mpinnuck/PiDjiRc2KmzSync/mechanical/Circuit/PiRCS2Updater/PiRCS2Updater-simple.kicad_sch

## KiCad design mechanical/Circuit/PiRCS2Updater/PiRCS2Updater-simple.kicad_sch (2026-10-04)

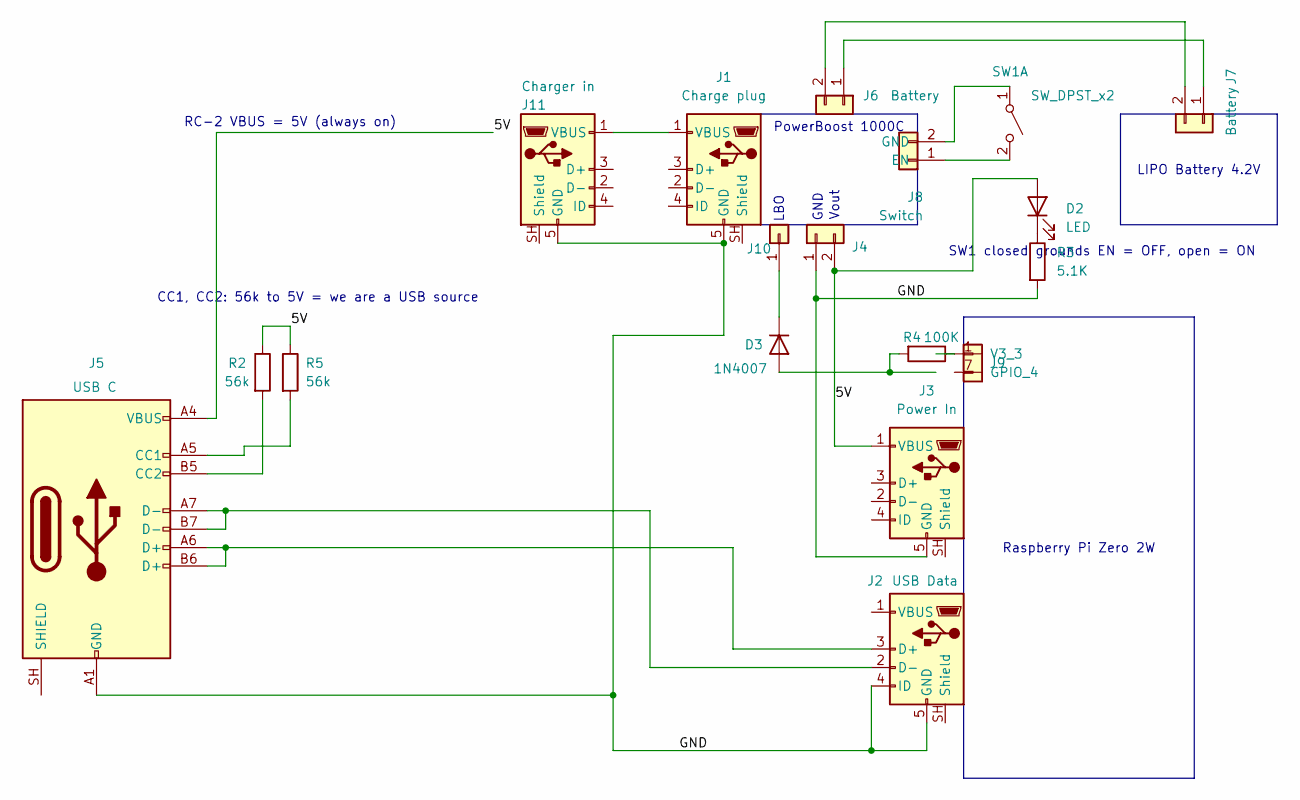
[picture p4: schematic PiRCS2Updater-simple.kicad_sch]

Parts:
D2: LED
D3: 1N4007; D_DO-41_SOD81_P10.16mm_Horizontal
J1: Charge plug
J2: USB Data
J3: Power In
J4, J9: Conn_01x02
J5: USB C
J6, J7: Battery
J8: Switch
J10: Conn_01x01
J11: Charger in
R2, R5: 56k
R3: 5.1K
R4: 100K
SW1: SW_DPST_x2

Connections:
5V: D2.2 (A), J3.1 (VBUS), J4.2, J5.A4 (VBUS), J5.A9 (VBUS), J5.B4 (VBUS), J5.B9 (VBUS), R2.1, R5.1
GND: J1.5 (GND), J2.4 (ID), J2.5 (GND), J3.5 (GND), J4.1, J5.A1 (GND), J5.A12 (GND), J5.B1 (GND), J5.B12 (GND), J11.5 (GND), R3.2
unnamed: D2.1 (K), R3.1
unnamed: D3.1 (K), J10.1
unnamed: D3.2 (A), R4.2
unnamed: J1.1 (VBUS), J11.1 (VBUS)
unnamed: J2.2 (D-), J5.A7 (D-), J5.B7 (D-)
unnamed: J2.3 (D+), J5.A6 (D+), J5.B6 (D+)
unnamed: J5.A5 (CC1), R5.2
unnamed: J5.B5 (CC2), R2.2
unnamed: J6.1, J7.1
unnamed: J6.2, J7.2
unnamed: J8.1 (EN), SW1.2 (B)
unnamed: J8.2 (GND), SW1.1 (A)
unnamed: J9.1 (V3_3), R4.1

Notes on the sheet:
SW1 closed grounds EN = OFF, open = ON
GND
RC-2 VBUS = 5V (always on)
Vout
LBO
Raspberry Pi Zero 2W
PowerBoost 1000C
LIPO Battery 4.2V
CC1, CC2: 56k to 5V = we are a USB source
