mpinnuck/PiDjiRc2KmzSync/mechanical/Circuit/PiRCS2Updater/PiRCS2Updater.kicad_sch

## KiCad design mechanical/Circuit/PiRCS2Updater/PiRCS2Updater.kicad_sch (2026-09-25)

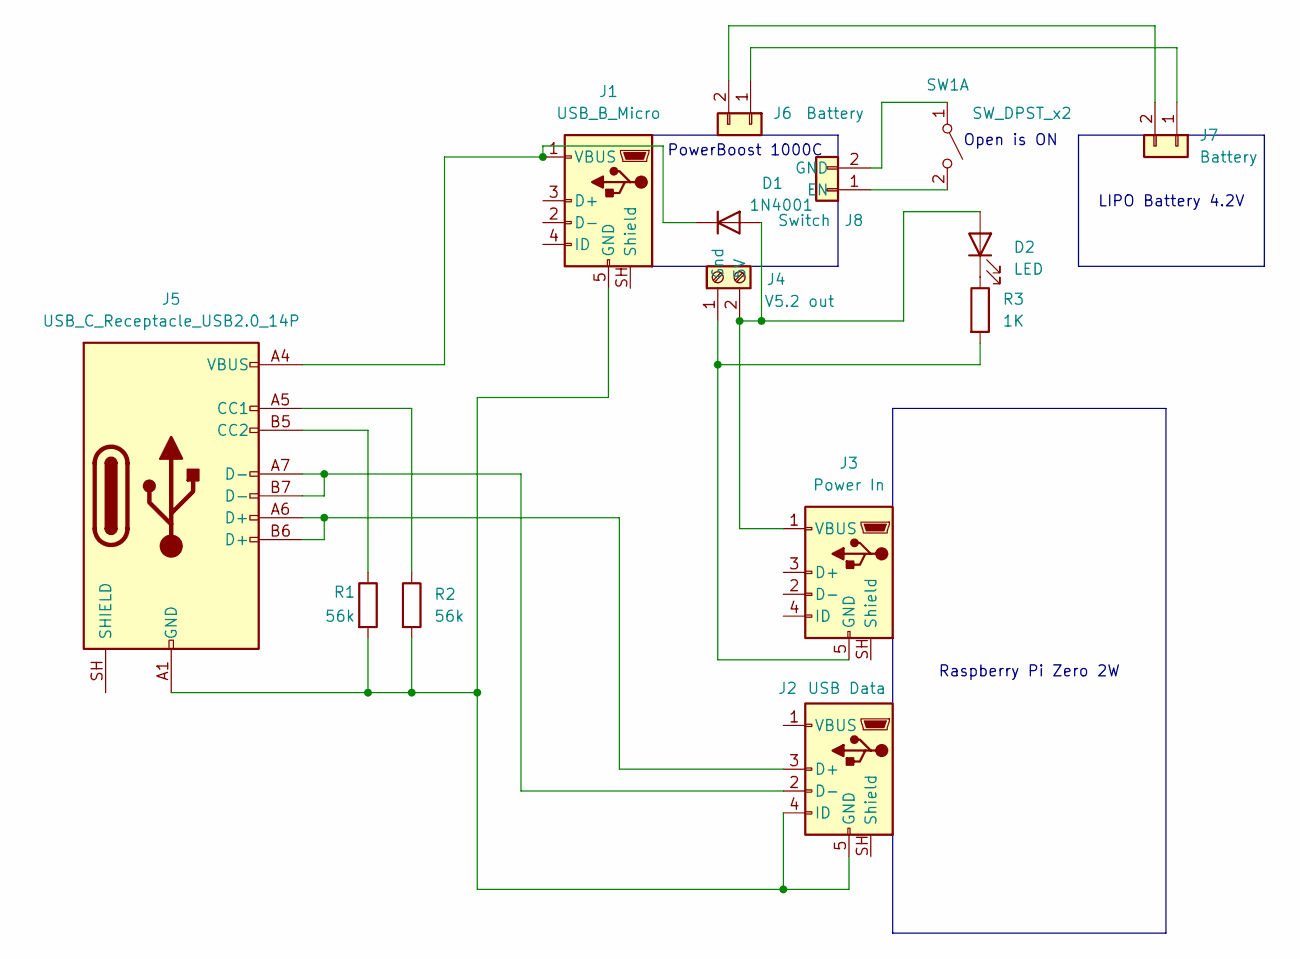
[picture p5: schematic PiRCS2Updater.kicad_sch]

Parts:
D1: 1N4001; D_DO-41_SOD81_P10.16mm_Horizontal
D2: LED
J1: USB_B_Micro
J2: USB Data
J3: Power In
J4: V5.2 out
J5: USB_C_Receptacle_USB2.0_14P
J6, J7: Battery
J8: Switch
R1, R2: 56k
R3: 1K
SW1: SW_DPST_x2

Connections:
unnamed: D1.1 (K), J1.1 (VBUS), J5.A4 (VBUS), J5.A9 (VBUS), J5.B4 (VBUS), J5.B9 (VBUS)
unnamed: D1.2 (A), D2.2 (A), J3.1 (VBUS), J4.2 (5V)
unnamed: D2.1 (K), R3.1
unnamed: J1.5 (GND), J2.4 (ID), J2.5 (GND), J5.A1 (GND), J5.A12 (GND), J5.B1 (GND), J5.B12 (GND), R1.2, R2.2
unnamed: J2.2 (D-), J5.A7 (D-), J5.B7 (D-)
unnamed: J2.3 (D+), J5.A6 (D+), J5.B6 (D+)
unnamed: J3.5 (GND), J4.1 (Gnd), R3.2
unnamed: J5.A5 (CC1), R2.1
unnamed: J5.B5 (CC2), R1.1
unnamed: J6.1, J7.1
unnamed: J6.2, J7.2
unnamed: J8.1 (EN), SW1.2 (B)
unnamed: J8.2 (GND), SW1.1 (A)

Notes on the sheet:
Open is ON
Raspberry Pi Zero 2W
PowerBoost 1000C
LIPO Battery 4.2V
