mpinnuck/PiDjiRc2KmzSync/mechanical/Circuit/PiRCS2Updater/xPiRCS2Updater.kicad_sch

## KiCad design mechanical/Circuit/PiRCS2Updater/xPiRCS2Updater.kicad_sch (2026-10-04)

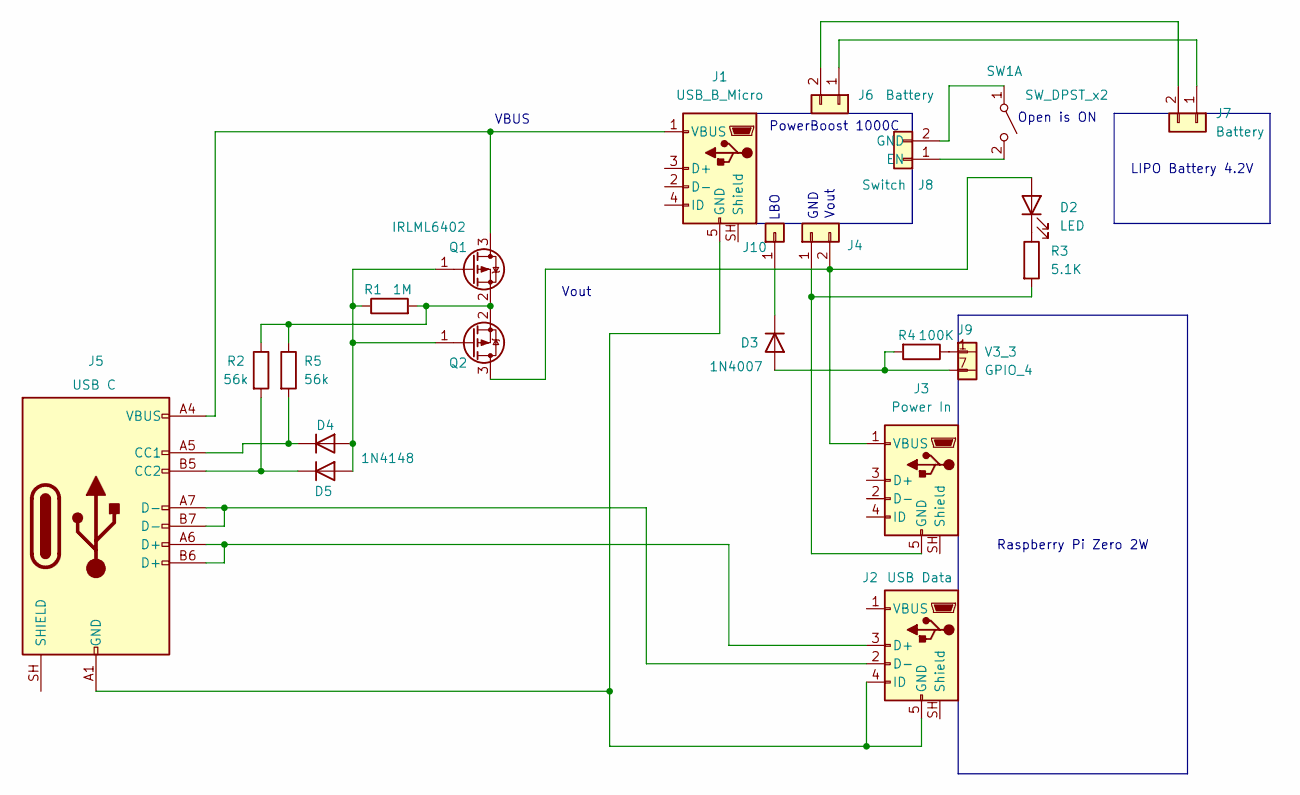
[picture p6: schematic xPiRCS2Updater.kicad_sch]

Parts:
D2: LED
D3: 1N4007; D_DO-41_SOD81_P10.16mm_Horizontal
D4, D5: 1N4148; D_DO-35_SOD27_P7.62mm_Horizontal
J1: USB_B_Micro
J2: USB Data
J3: Power In
J4, J9: Conn_01x02
J5: USB C
J6, J7: Battery
J8: Switch
J10: Conn_01x01
Q1, Q2: IRLML6402; SOT-23
R1: 1M
R2, R5: 56k
R3: 5.1K
R4: 100K
SW1: SW_DPST_x2

Connections:
unnamed: D2.1 (K), R3.1
unnamed: D2.2 (A), J3.1 (VBUS), J4.2
unnamed: D3.1 (K), J10.1
unnamed: D3.2 (A), J9.7 (GPIO_4), R4.2
unnamed: D4.1 (K), J5.A5 (CC1), R5.2
unnamed: D4.2 (A), D5.2 (A), Q1.1 (G), Q2.1 (G), R1.1
unnamed: D5.1 (K), J5.B5 (CC2), R2.2
unnamed: J1.1 (VBUS), J5.A4 (VBUS), J5.A9 (VBUS), J5.B4 (VBUS), J5.B9 (VBUS), Q1.3 (D)
unnamed: J1.5 (GND), J2.4 (ID), J2.5 (GND), J5.A1 (GND), J5.A12 (GND), J5.B1 (GND), J5.B12 (GND)
unnamed: J2.2 (D-), J5.A7 (D-), J5.B7 (D-)
unnamed: J2.3 (D+), J5.A6 (D+), J5.B6 (D+)
unnamed: J3.5 (GND), J4.1, R3.2
unnamed: J6.1, J7.1
unnamed: J6.2, J7.2
unnamed: J8.1 (EN), SW1.2 (B)
unnamed: J8.2 (GND), SW1.1 (A)
unnamed: J9.1 (V3_3), R4.1
unnamed: Q1.2 (S), Q2.2 (S), R1.2, R2.1, R5.1

Notes on the sheet:
Open is ON
GND
Vout
VBUS
Vout
LBO
Raspberry Pi Zero 2W
PowerBoost 1000C
LIPO Battery 4.2V
